mgj0721/Digital_Twin/IMG_0704.JPG

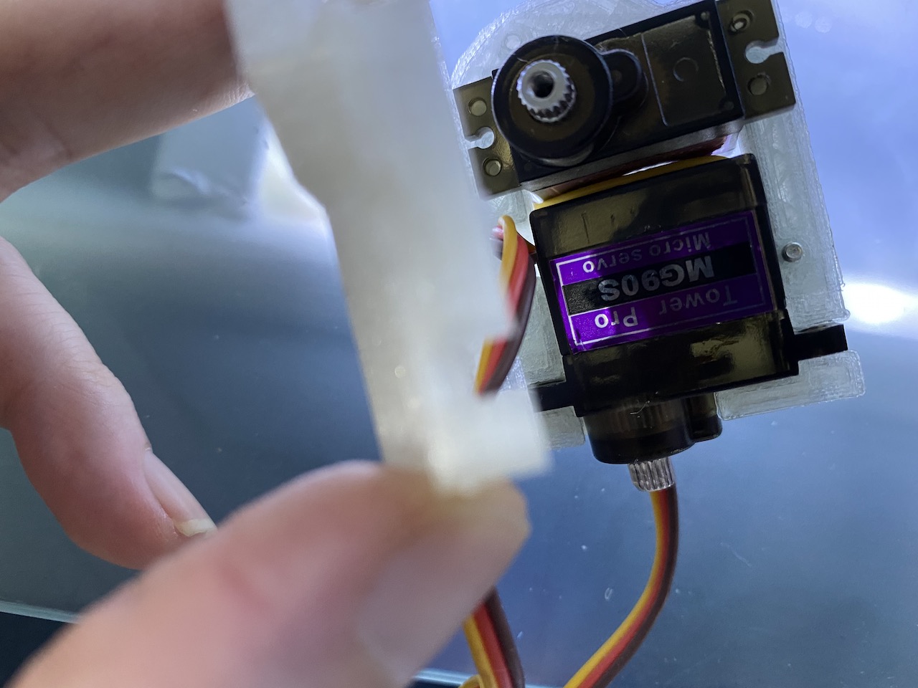
IMG_0704.JPG
