mgj0721/Digital_Twin/PanTilt1.jpg

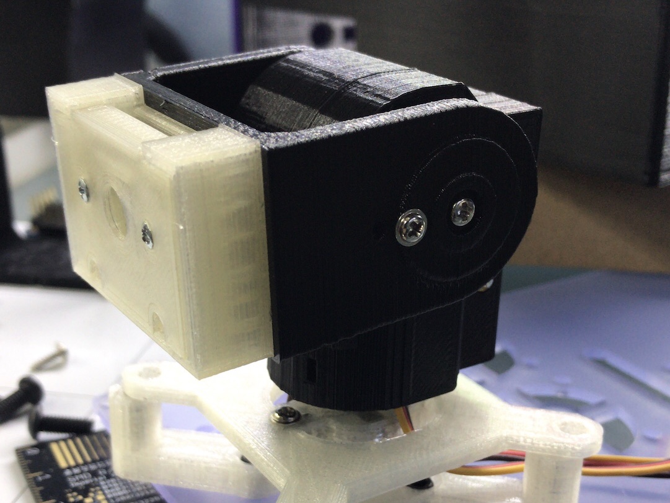
PanTilt1.jpg
