mgj0721/Digital_Twin/PanTilt2.jpg

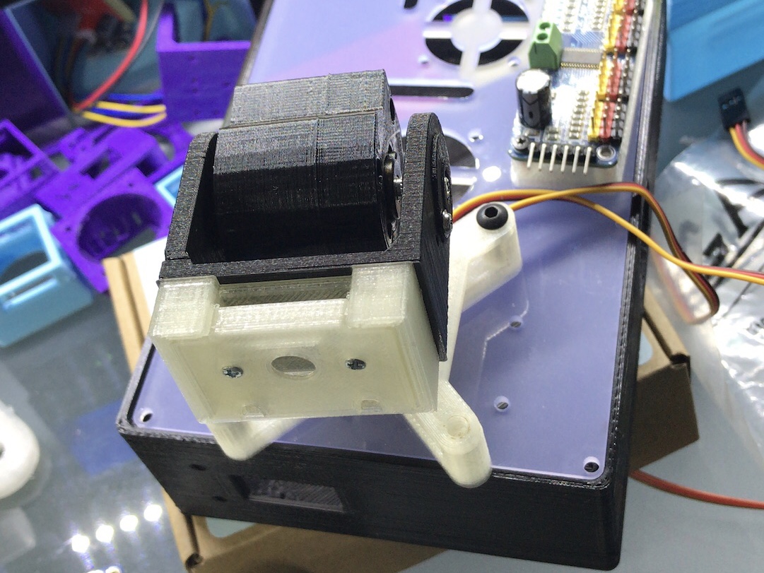
PanTilt2.jpg
