mgj0721/Digital_Twin/PanTilt5.jpg

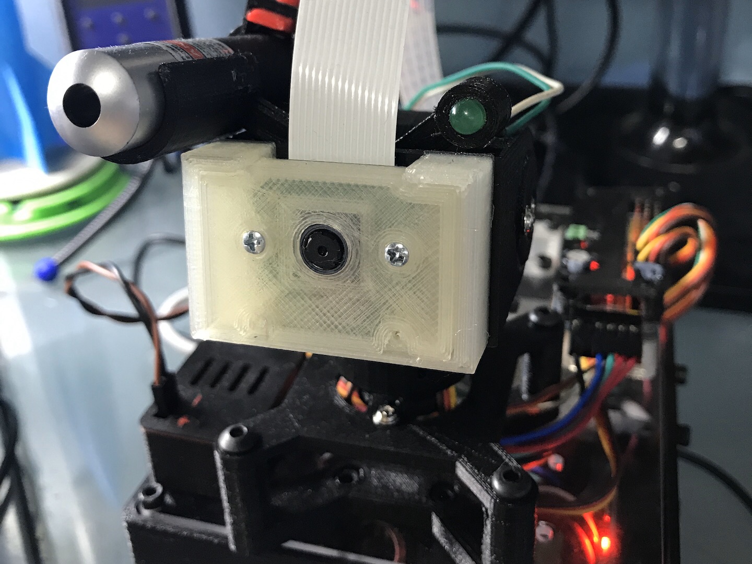
PanTilt5.jpg
