mgj0721/Digital_Twin/PanTilt_Base.png

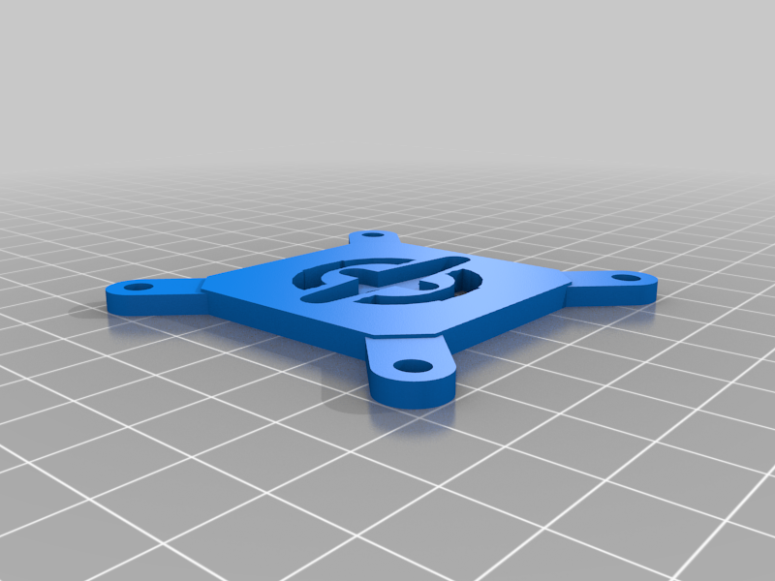
PanTilt_Base.png
