mgj0721/Digital_Twin/PanTilt_Baselock.png

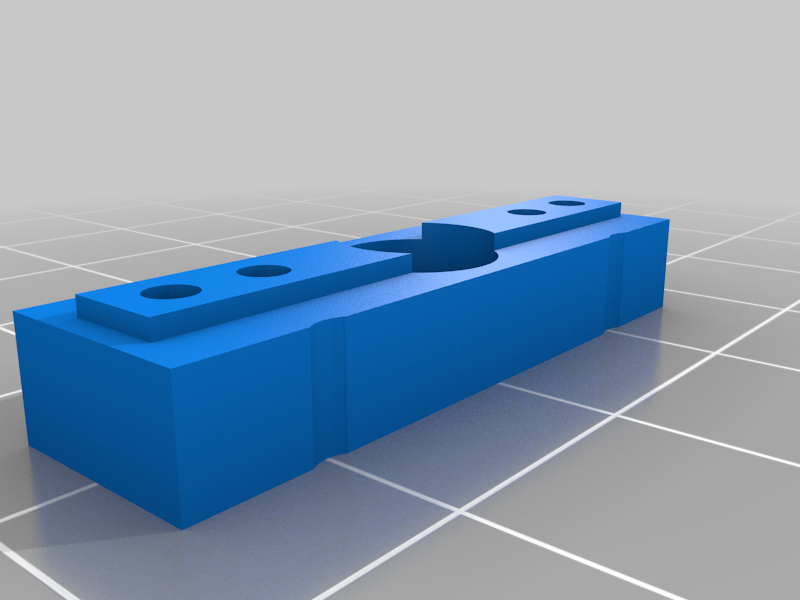
PanTilt_Baselock.png
