mgj0721/Digital_Twin/PanTilt_Block.png

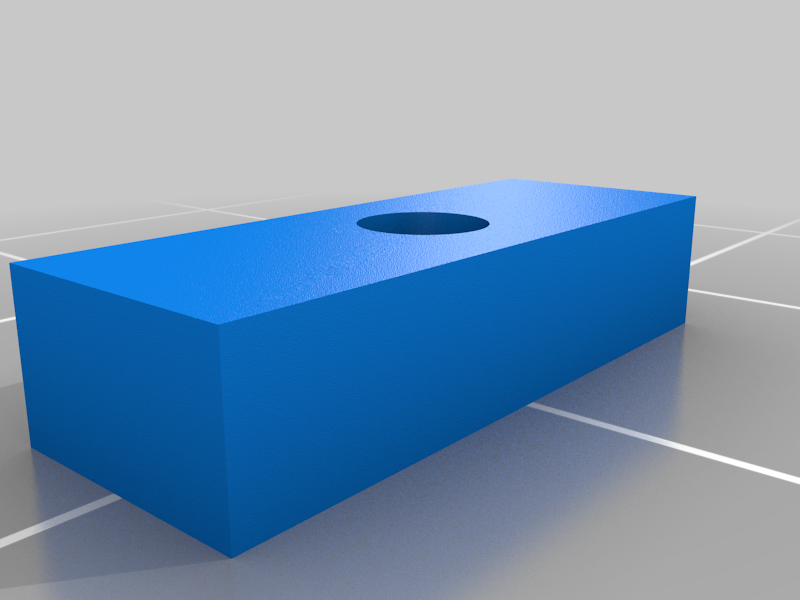
PanTilt_Block.png
