mgj0721/Digital_Twin/PanTilt_Body-A.png

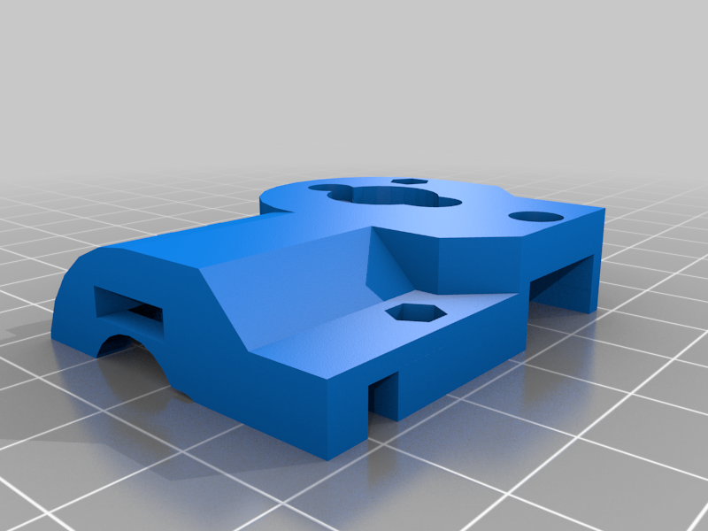
PanTilt_Body-A.png
