mgj0721/Digital_Twin/PanTilt_Body-B.png

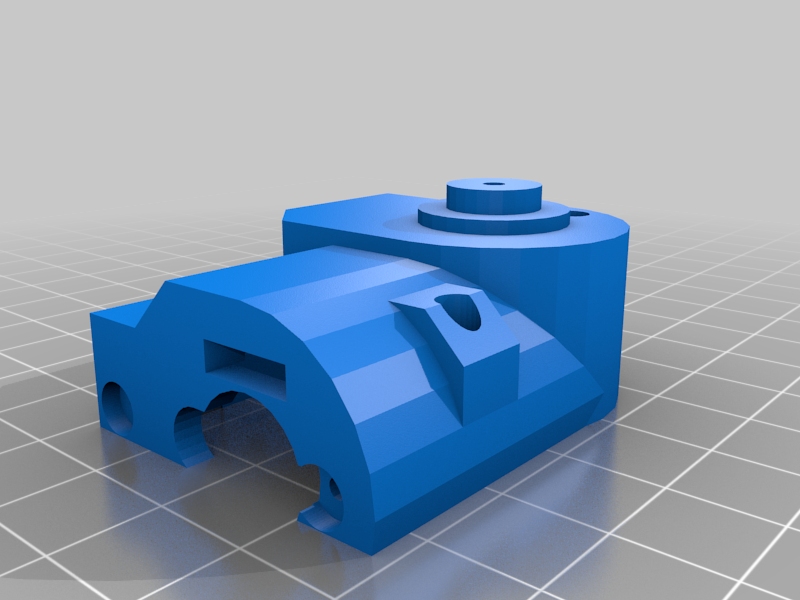
PanTilt_Body-B.png
