mgj0721/Digital_Twin/PanTilt_Camerabottom.png

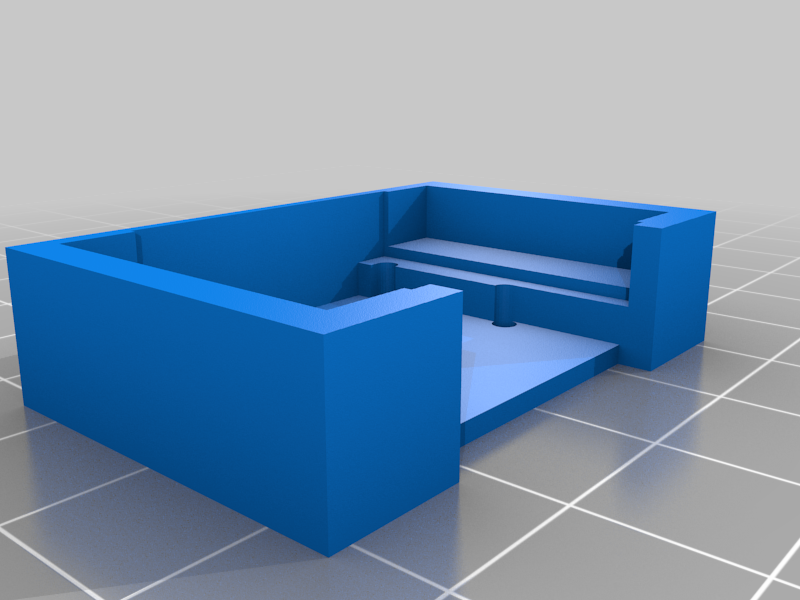
PanTilt_Camerabottom.png
