mgj0721/Digital_Twin/PanTilt_Baselock.stl

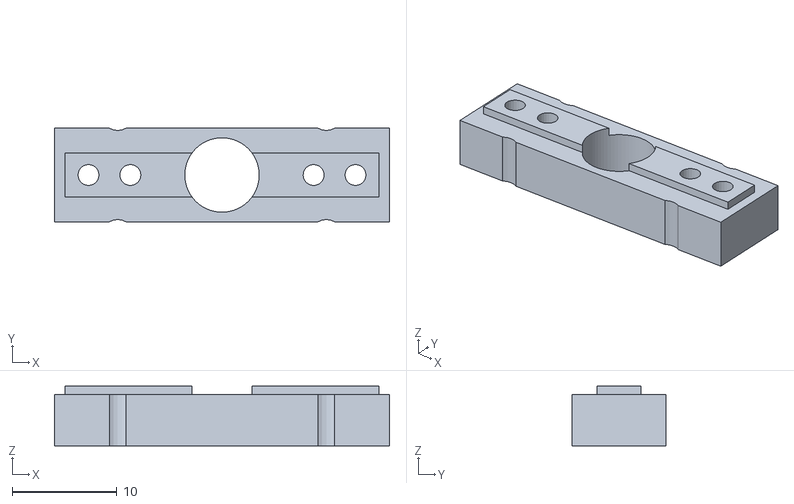
[picture p31: CAD file, 2026-09-03]
PanTilt_Baselock.stl
32.0 x 8.99 x 5.70
